Onyme13/Homemade_Glider_Tracker/positions_functions.py

"""File that has multiple functions in link with the position of the glider"""
import math
import os
import datetime



#Function that define the oritentation of the glider (360°) betwenn two positions
def orient(position_list):

    if len(position_list) >= 2:

        old_latitude = position_list[-2][0]
        old_longitude = position_list[-2][1]
        new_latitude = position_list[-1][0]
        new_longitude = position_list[-1][1]


        old_latitude = math.radians(old_latitude)
        old_longitude = math.radians(old_longitude)
        new_latitude = math.radians(new_latitude)
        new_longitude = math.radians(new_longitude)

        delta_latitude = new_latitude - old_latitude
        delta_longitude = new_longitude - old_longitude

        direction = math.degrees(math.atan2(delta_longitude, delta_latitude))

        direction = (direction + 360) % 360

        return direction
    else:
        return 0



# Function that stores the last known postion in CSV file
def write_last_positon(lat,long):
    with open("data/last_pos.csv", "w") as f:
        f.write(str(lat)+","+str(long))

# Function that reads the last known postion from the CSV file from the write_last_positon function
def read_last_positon():
    with open("data/last_pos.csv", "r") as f:
        lat,long = f.readline().split(",")
        return float(lat),float(long)

# Function that writes positions in a csv file for later flight position analysis
def write_mouvement(lat,long,alt,time):
    current_date = datetime.datetime.now().date()

    formatted_date = current_date.strftime("%Y-%m-%d")
    file_name = "mouvment_"+formatted_date+".csv"
    if not os.path.exists("data/"+file_name):
        with open("data/"+file_name, "w") as f:
            f.write("lat,long,alt,time\n")
    with open("data/"+file_name, "a") as f:
        f.write(str(lat)+","+str(long)+","+str(alt)+","+str(time)+"\n")
        f.close()
        
        
