Onyme13/Homemade_Glider_Tracker/constants.py

"""Python file containing constants for performance optimisation"""

#UI
BLACK = '#000000'
WHITE = '#FFFFFF'
FONT = ('Regular',13)

#main
SEALEVELPRESSURE = 1013.25 
METERSOFAIRHETCOPASCAL = 0.12677457000000025
HETCOPASCALMETERSOFAIR = 7.8880172892718
FEETSPERMETER = 3.28084
